frebbles/tankmon/tankmon-cases/us_case_plug.scad

use <shaft_mount_func.scad>

cyl_rail_case_plug(46,21,2);
